saper-2/esp8266-osk103/photos/EPS8266-OSK103v2-RIG-PogoPins2.jpg

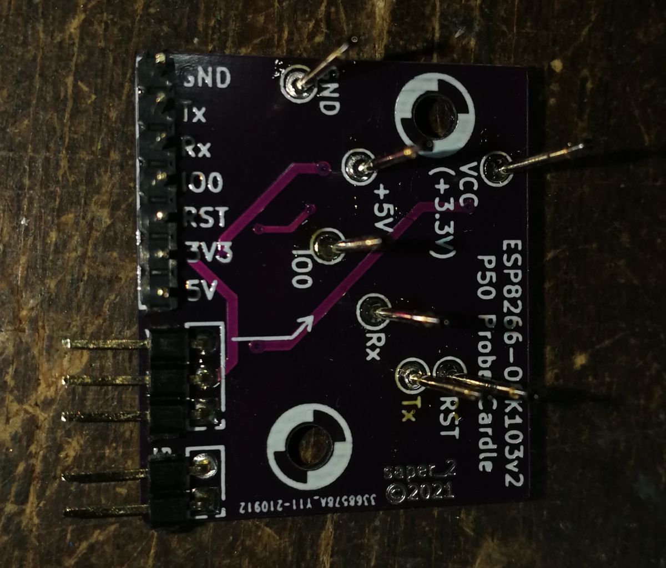
photos/EPS8266-OSK103v2-RIG-PogoPins2.jpg
