saper-2/esp8266-osk103/photos/EPS8266-OSK103v2-RIG-PogoPins3.jpg

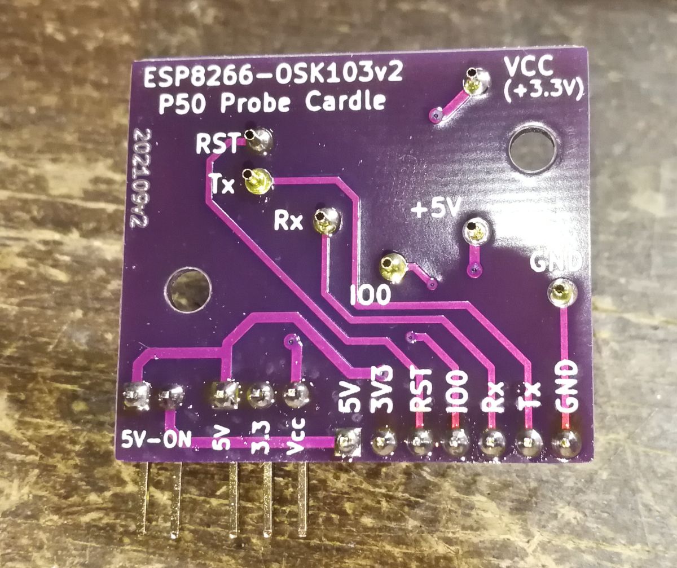
photos/EPS8266-OSK103v2-RIG-PogoPins3.jpg
