saper-2/esp8266-osk103/photos/remove-usb-insert-grab.jpg

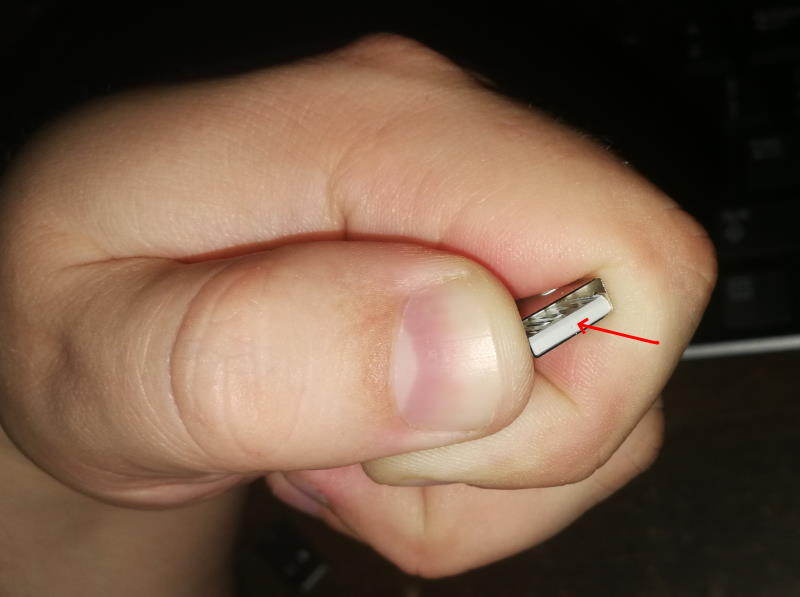
photos/remove-usb-insert-grab.jpg
