saper-2/esp8266-osk103/photos/RIG-2.jpg

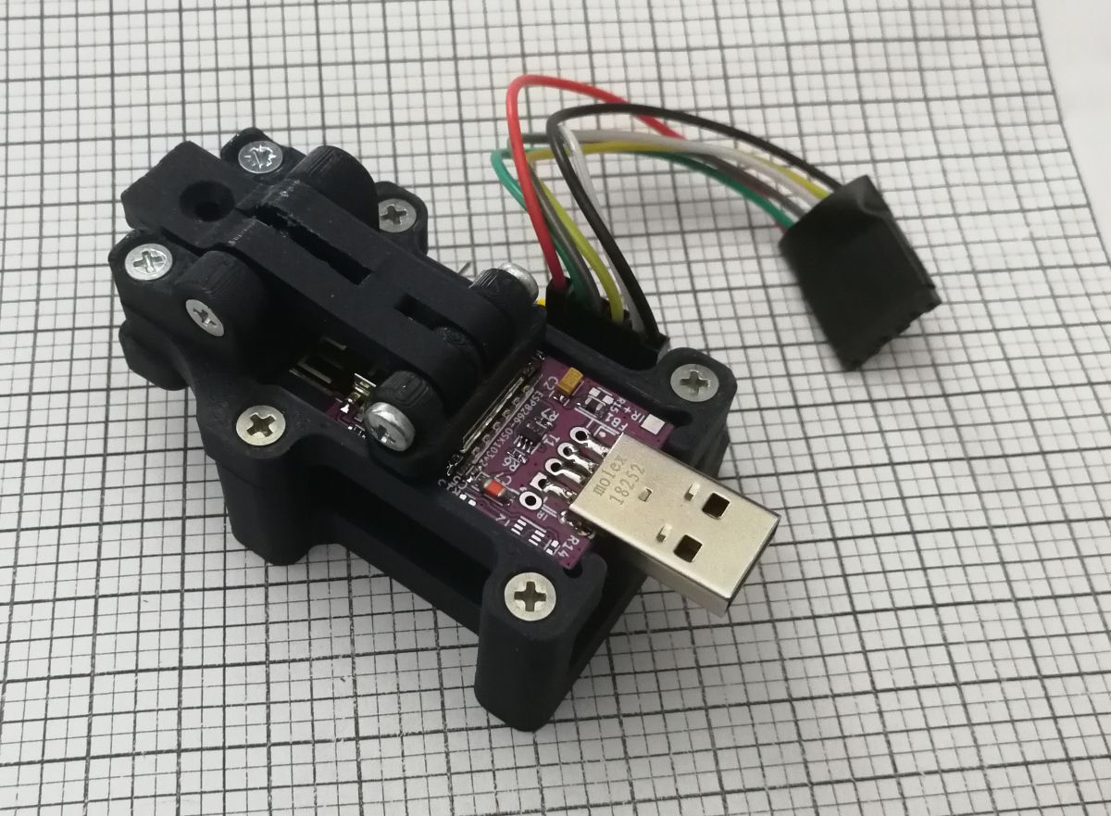
photos/RIG-2.jpg
