saper-2/esp8266-osk103/photos/RIG-3.jpg

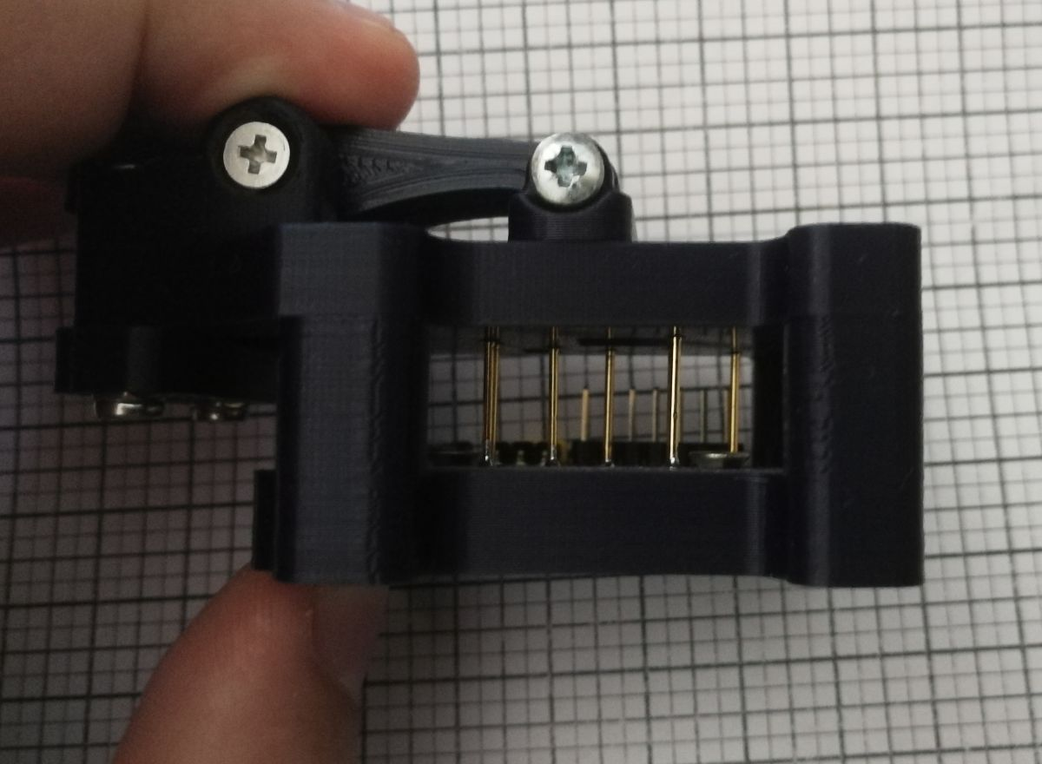
photos/RIG-3.jpg
