saper-2/esp8266-osk103/photos/RIG-6.jpg

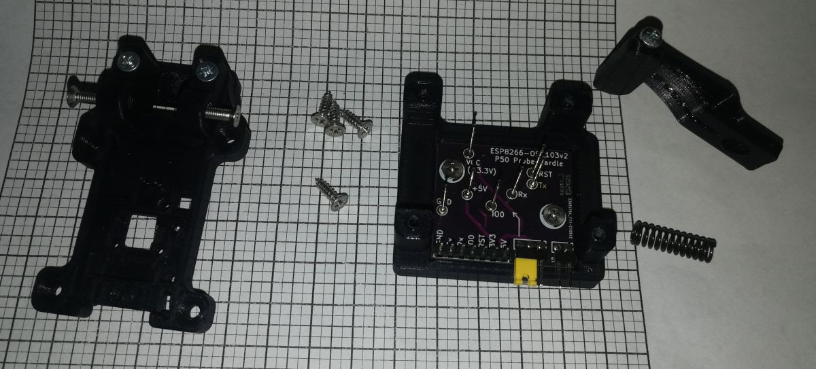
photos/RIG-6.jpg
