saper-2/esp8266-osk103/photos/RIG-7.jpg

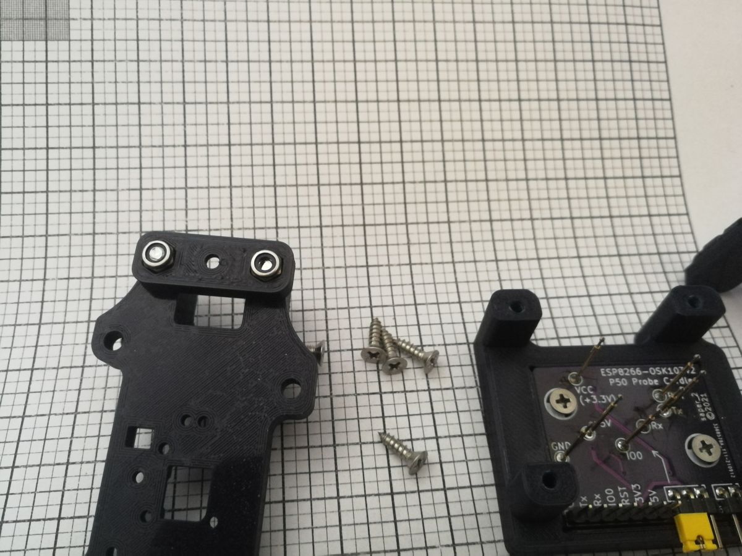
photos/RIG-7.jpg
