saper-2/esp8266-osk103/photos/usb-insert-cut.jpg

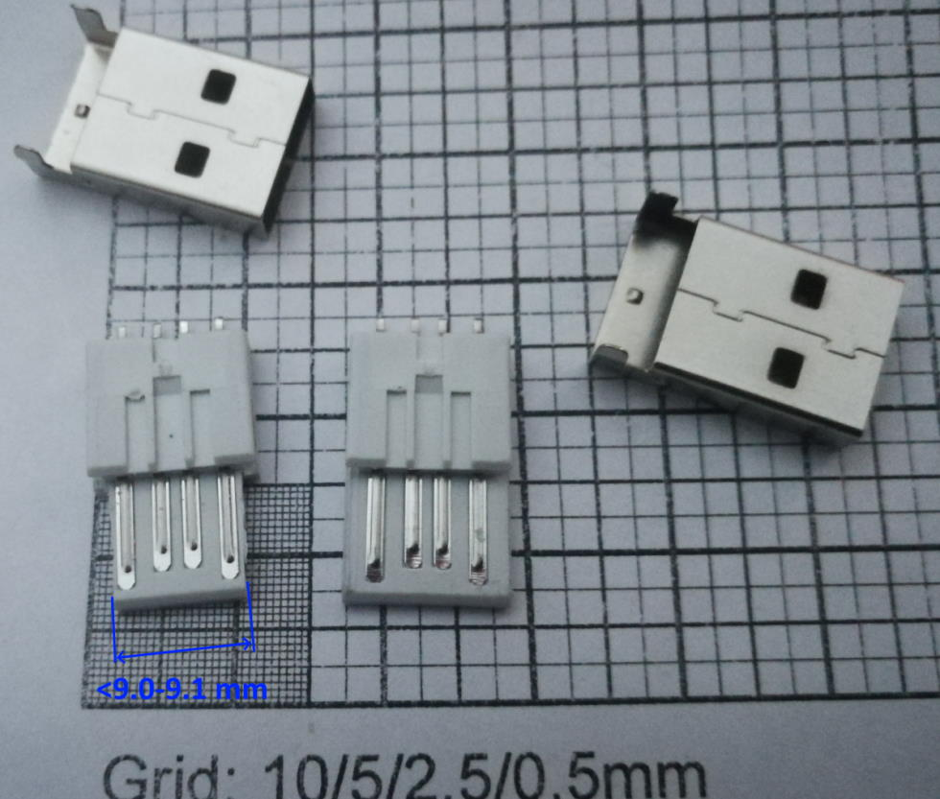
photos/usb-insert-cut.jpg
